AG6GR/ColorGlove/LED_Driver.asc

D1: diode
D2: diode
D3: diode
Q1: npn; 2N2222
Q2: pnp; 2N3906
R1: res; 100
R2: res; 100k
R3: res; 10k
V1: voltage; PULSE(0 3.3 1 0 0 1 2 5)
V2: voltage; 5
Named nets: 0
.tran 10
